TheCaveCz/kit-dice/doc/pictures/1.jpg

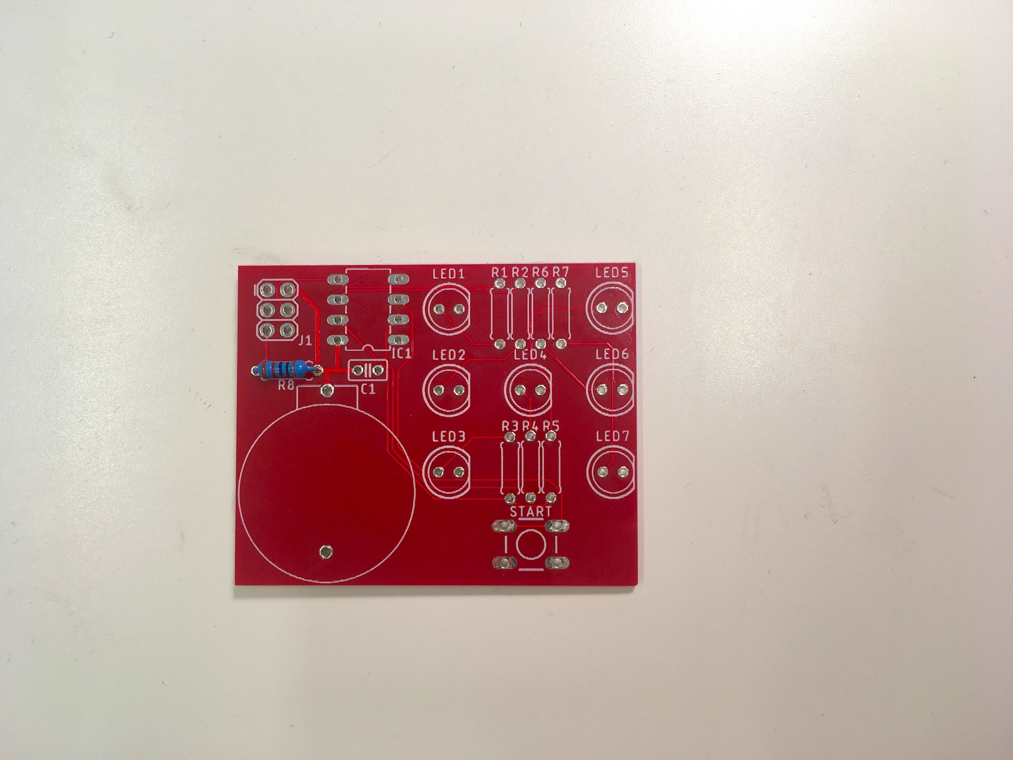
doc/pictures/1.jpg
