TheCaveCz/kit-dice/doc/pictures/2.jpg

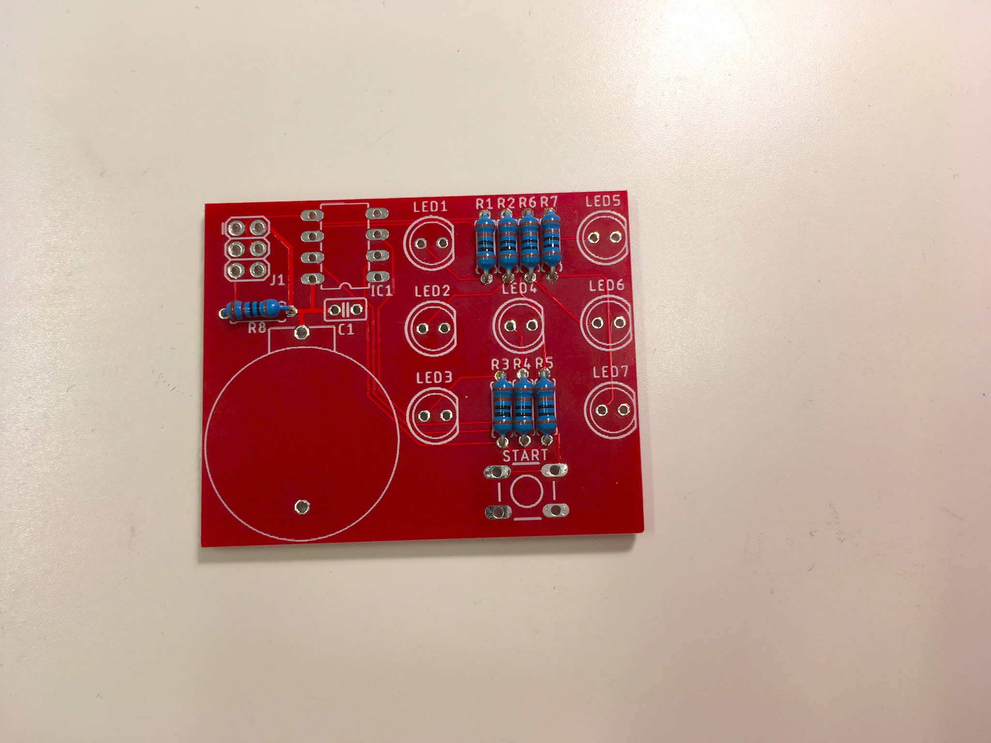
doc/pictures/2.jpg
