TheCaveCz/kit-dice/doc/pictures/3.jpg

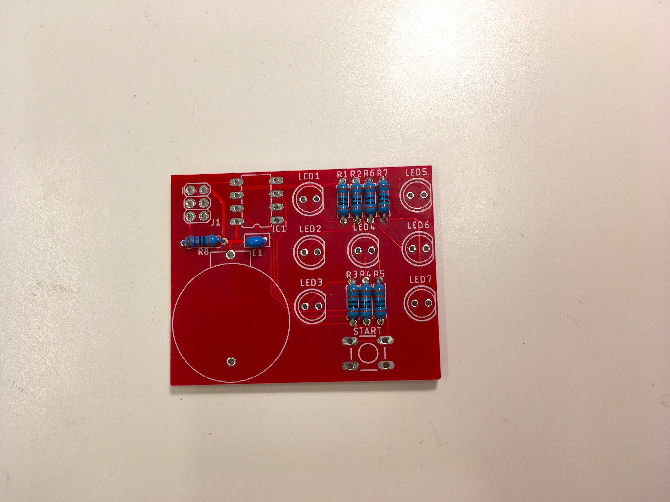
doc/pictures/3.jpg
