TheCaveCz/kit-dice/doc/pictures/4.jpg

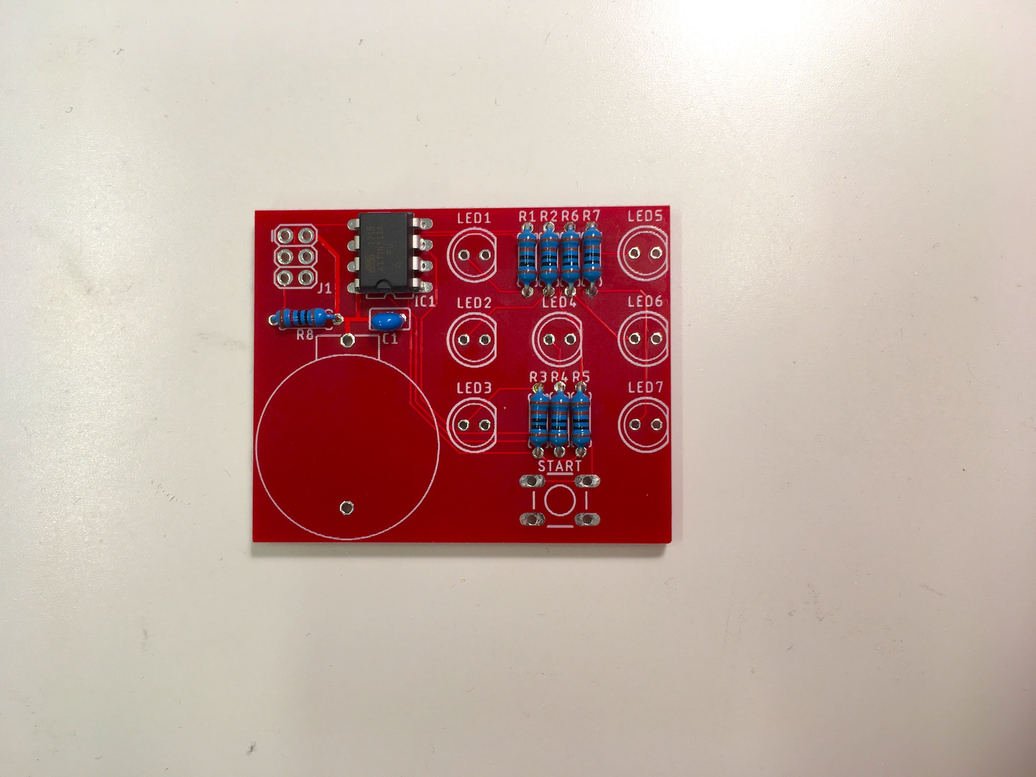
doc/pictures/4.jpg
