TheCaveCz/kit-dice/doc/pictures/5.jpg

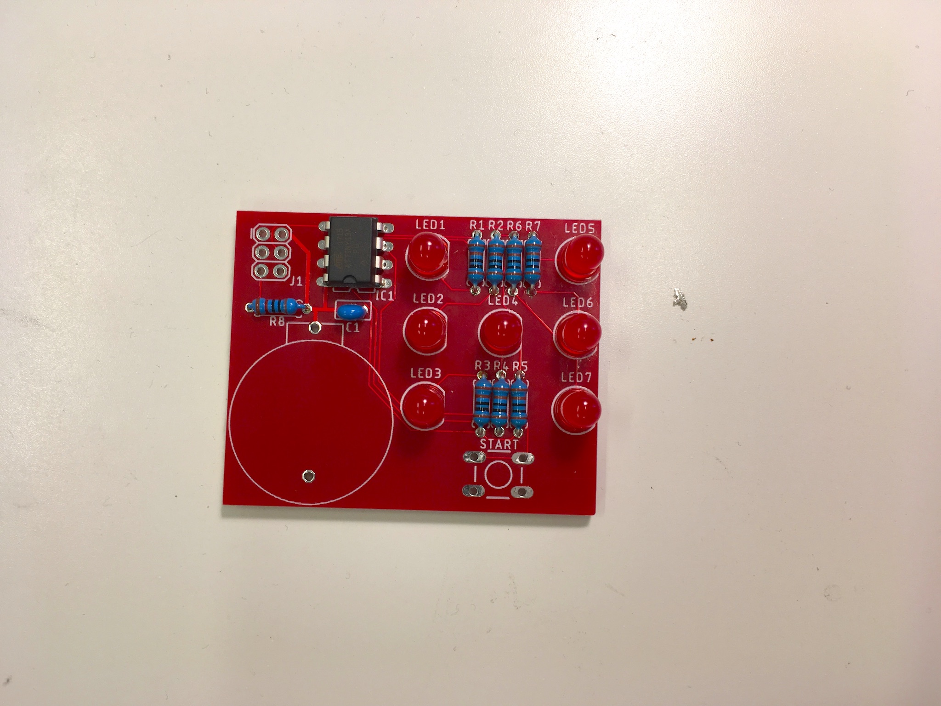
doc/pictures/5.jpg
