TheCaveCz/kit-dice/doc/pictures/6.jpg

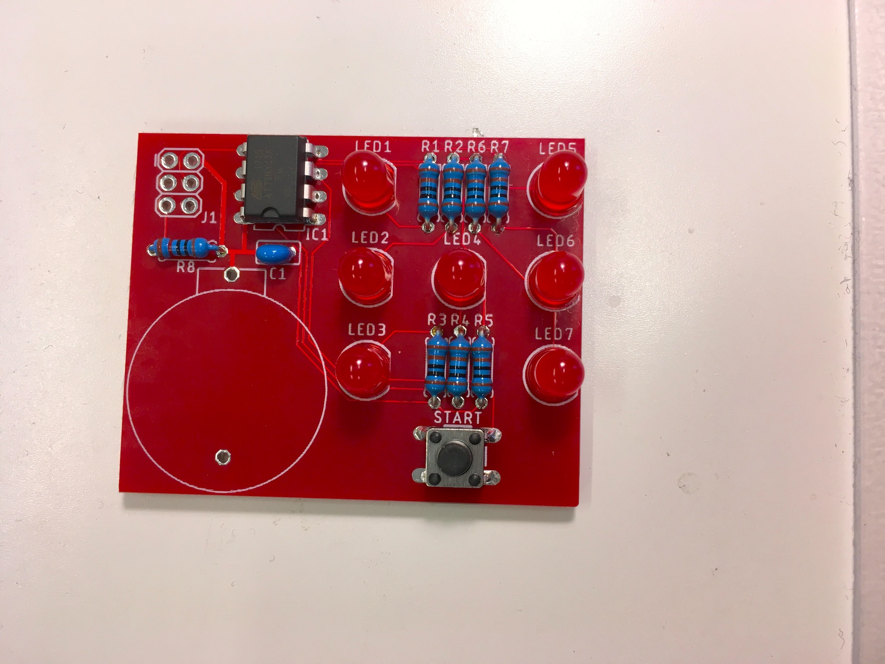
doc/pictures/6.jpg
