TheCaveCz/kit-dice/doc/pictures/7.jpg

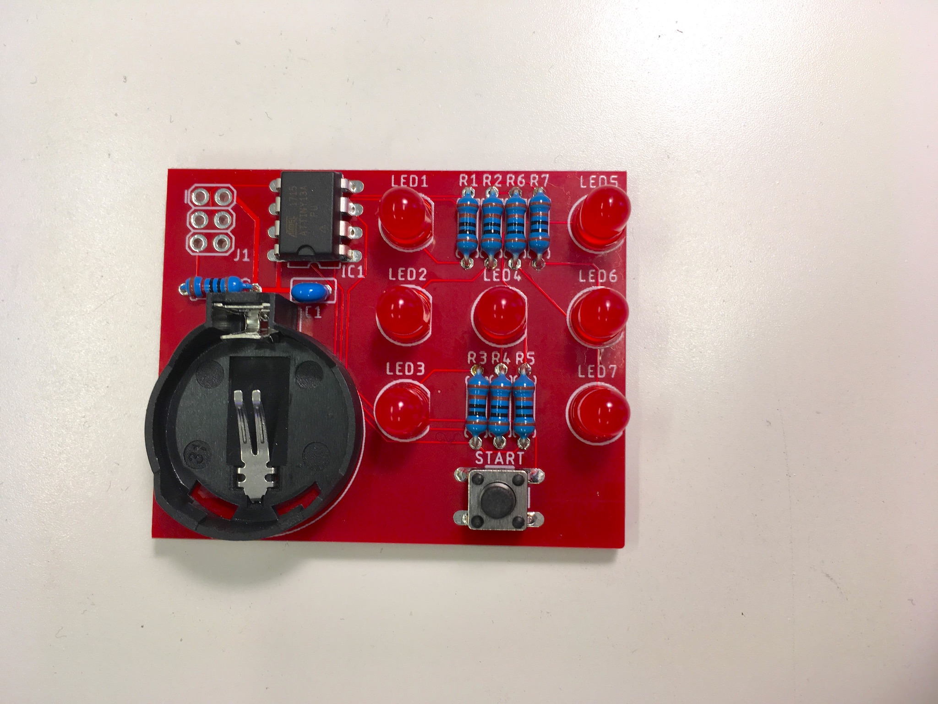
doc/pictures/7.jpg
