TheCaveCz/kit-dice/doc/pictures/kit.jpg

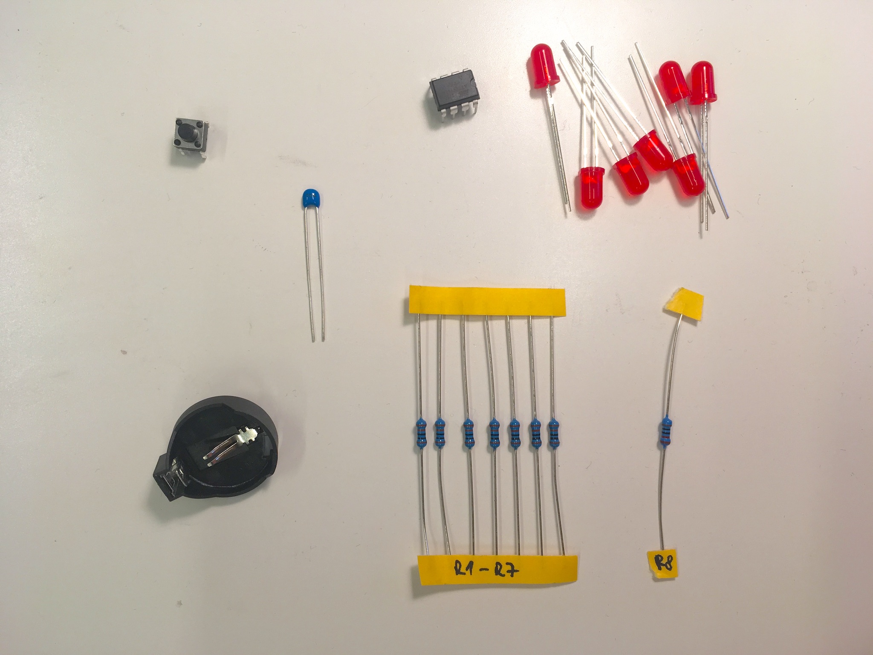
doc/pictures/kit.jpg
