TheCaveCz/kit-dice/doc/pictures/manual-cz-3.jpeg

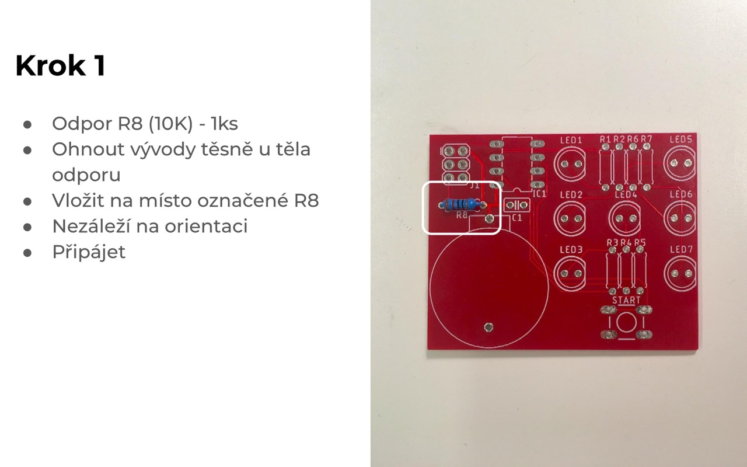
doc/pictures/manual-cz-3.jpeg
